jmprovencher/Treasure-Picker-Robot/Remises/Remise 1/tex/Sylvain/systeme_mecanique.tex

La base mécanique du robot est assurée par les différentes plate-formes et tiges filetées fournies pour le projet, il en revient donc à nous de décider de l'agencement de ces composantes afin de produire un robot mécaniquement efficace. De manière à bien modéliser le robot et ainsi faciliter l'installation de futurs équipements, il fut décidé de réaliser une représentation 3D du prototype. La figure \ref{f:CAD} présente le dessin ainsi réalisé, bien que grossier il fut construit à partir de mesures exactes effectuées sur le robot. Ce dessin est très utile pour planifier d'avance l'emplacement des différents systèmes qui seront ajoutés au cours du projet en plus de permettre une meilleure planification de l'organisation des circuits électroniques. 

\medbreak

On peut remarquer que sur ce dessin l'ordinateur embarqué est situé sur la plate-forme centrale, ce choix est justifié par le fait que nous désirons avoir l'électronique le plus proche possible des moteurs DC afin de limiter la longueur des fils. La batterie LiPO représentée par le bloc bleu est positionnée sur la plate-forme la plus basse de manière à assurer un centre de gravité assez bas. Le bloc jaune représente environ les dimensions des circuits électroniques présents sur cet étage du robot. Bien évidemment, toutes ces composantes seront fixées en place. Bien que le pont en H n'est pas observable sur cette image il est important de noter que celui-ci peut être fixé sous la base en cas de besoin. Le préhenseur présenté à la section \ref{s:Prehenseur} est représenté sur le devant du robot, la caméra embarquée est installée directement au-dessus de ce dispositif sur l'étage le plus haut. L'utilisation de ce dessin 3D et d'un autre dessin de la borne de rechargement a aussi permis de mesurer, sans faire de prototype de préhenseur, la hauteur adéquate de la bobine de chargement du condensateur afin de bien aligner les deux dispositifs.

\begin{figure}[htp]
   \centering
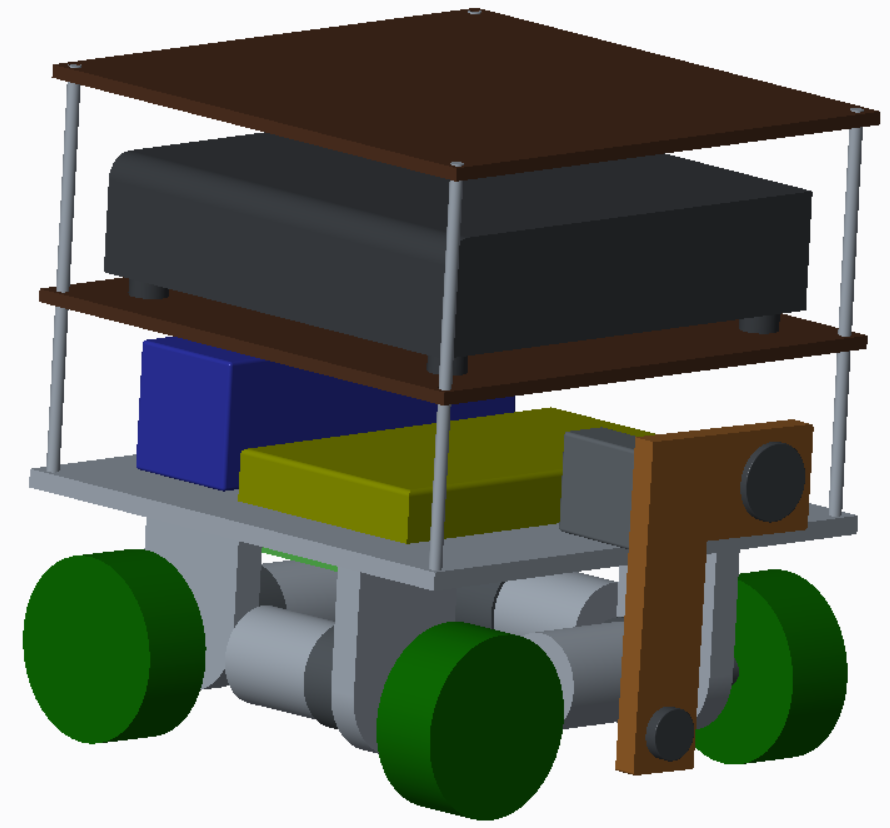
[picture p6: Remises/fig/ROBOT.png]
   
   \caption{Représentation 3D du robot}
   \label{f:CAD}
\end{figure}
