jmprovencher/Treasure-Picker-Robot/Remises/Remise 1/tex/Bourque/comm_sans_fil.tex

La transmission sans-fil du code Manchester est assurée par une combinaison LED-photorécepteur. La LED est située sur le dessus de la station de recharge et le photorécepteur est situé sur le dessus du robot. Ce système de communication sans-fil est limité à des distances relativement faibles, mais le robot étant en contact physique avec la station de recharge, cette contrainte ne pose pas de problème. Le dessin 3D présenté précédemment servira à planifier la disposition exacte de ces composantes une fois les pièces reçues et le concept testé de manière à minimiser les temps de construction et d'assemblage.

\medbreak

La LED est modulé par un microcontrôleur situé sur la station de recharge. Le modèle du microcontrôleur reste à déterminer, mais devra être assez simple et peu coûteux puisque sa tâche sera relativement simple. Ce système de communication est illustré sur le schéma \ref{f:led_robot}.

\medbreak

Le document \cite{COM00} explique brièvement comment réaliser un tel système et est utilisé comme référence pour réaliser notre système.

\begin{figure}[htp]
	\centering
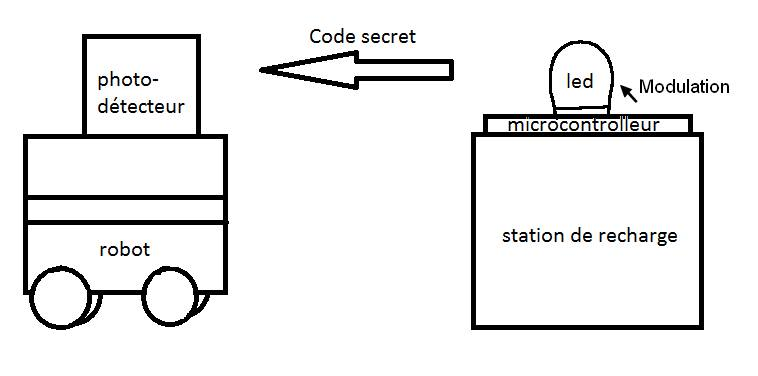
[picture p7: Remises/fig/led_robot.png]
	
	\caption{Communication sans-fil entre la station de recharge et le robot}
	\label{f:led_robot}
\end{figure}
