jmprovencher/Treasure-Picker-Robot/Remises/Remise 1/tex/Main/liste_pieces.tex

\begin{description}
\label{liste_pieces}
	\item[Buck (x3)] \url{http://www.ebay.ca/itm/171445007919?_trksid=p2050601.m570.l6004&_trkparms=gh1g\%3DI171445007919.N41.S2.R2.TR2}
	\item[Batterie LiPo] \url{http://www.hobbyking.com/hobbyking/store/__10284__Turnigy_4500mAh_6S_30C_Lipo_Pack.html}
	\item[Chargeur de batterie LiPO] \url{http://www.hobbyking.com/hobbyking/store/__40270__Hobbyking_8482_T682_AC_6s_10A_90W_Eco_Touch_Balance_Charger_Discharger.html}
	\item[Alarme batterie] \url{http://www.hobbyking.com/hobbyking/store/__74024__HobbyKing_8482_Lipo_Voltage_Checker_2S_8S_.html}
	\item[Arduino Mega] \url{http://www.robotshop.com/ca/en/arduino-mega-2560-microcontroller-rev3.html}
	\item[Servomoteur de contrôle du préhenseur] \url{http://www.robotshop.com/ca/en/hitec-hs-485hb-servo-motor.html}
	\item[Shield pour <<driver>> les moteurs] \url{http://www.robotshop.com/ca/en/motor-shield-kit-arduino-v2.html}
	\item[Électroaimant \textit{Grove}] \url{http://www.seeedstudio.com/wiki/Grove_-_Electromagnet}
\end{description}
