jmprovencher/Treasure-Picker-Robot/Remises/Remise 2/pdf/ContextDiagram.pdf

Business Process Diagram1 Caméra Monde Caméra robot Dispositif de communication sans-fil Serveur des îles Station de base Affichage de la tension du condensateur Affichage de la position et orientation du robot Affichage de la lettre ASCII Affichage de la trajectoire planifiée Rotation des roues Affichage de la forme/couleur de l'île Manipulation du trésor Ordinateur embarqué Microcontrolleur Électroaimant Robot Saisie et relâchement Activation et désactivation Commande de direction/vitesse Appel des méthodes de déplacement par UART Réponse JSON contenant les informations de l'île cible Vidéo fournissant position des trésors, des îles et de la station de recharge Requête HTML utilisant le code | Visual Paradigm Standard Edition(Universite Laval)
