jmprovencher/Treasure-Picker-Robot/Remises/Remise 2/pdf/DPF.pdf

# Obtenir l'île cible Établir une trajectoire de

# Prendre des décisions de manière autonome

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
# Alimenter le robot de manière autonome

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
# Naviguer autour des îles

5

5

5

# Éviter contact avec les murs

5

5

# Communiquer sans fil entre les éléments du système

5

5

5

# Protéger l'alimentation du robot avec des fusibles et interrupteurs

5

# Alimenter la station de recharge avec alimentation 5V, 1A

5

5

# Respecter un budget maximal de 300$ (sans PCB)

4

2

3

# Actualiser affichage à une fréquence minimale de 0.2Hz

5

5

5

5

5

1

# Effectuer au moins une routine complète en dix minutes

2

4

3

4

3

3

3

# Affichage de la tension du condensateur en temps réel sur la station de base

5

5
Finir le projet d'ici le 17 avril.

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
# Afficher la position avec une précision de position minimalement de 15 centimètres

5

5

# Monter l'électronique du robot sur un PCB

4

4

3

4 Tension entre 21V et 30V | 1 seule permise

# Communiquer entre les éléments du

sécuritaire aux éléments du système | autonome | | | autonome | | de façon autonome | de la station de base | système
Afficher la tension des cellules de la batterie Signaler une alerte en cas de danger Alimenter adéquatement chaque élément du système Protéger adéquatement les composantes électroniques internes | Démarrer le robot sans intervention extérieure Confirmer le départ de la routine à partir de la station Confirmer la fin de l'exécution ainsi que le temps écoulé avec l'usager | Décoder le code Manchester Envoyer une requête au serveur des îles Interpréter la réponse du serveur en format JSON | Analyser les flux vidéo des deux caméras pour identifier la cible façon autonome Alimenter le robot avec une batterie Établir une trajectoire vers un trésor puis vers une île Déterminer la commande idéale pour suivre la trajectoire | Avancer le robot Tourner le robot | Saisir un trésor Soulever un trésor Déposer un trésor sur l'île prescrite | Recevoir la charge par induction Lire la tension aux bornes du condensateur Se retirer lorsque la charge est complète | Afficher les trajectoires ⁽prévue et réelle⁾ sur une image de la table Afficher la position et l'orientation du robot Afficher la tension aux bornes du condensateur Afficher la forme ou la couleur de l'île cible | Communiquer entre l'ordinateur du robot et le microcontrôlleur Communiquer sans fil entre l'ordinateur du robot et la station de base Recevoir sans fil le code Manchester Communiquer sans fil entre l'ordinateur du robot et le serveur d'îles

# Se déplacer de façon

# Manipuler les trésors Gérer le condensateur

# Fournir une alimentation adéquate et

# Fonctionner de façon

# Offrir une interface graphique à l'aide
