jmprovencher/Treasure-Picker-Robot/Remises/Remise 3/tex/Main/annexe.tex

%!TEX encoding = IsoLatin

%
% Annexe "Liste des sigles et des acronymes"
%

\chapter{Liste des sigles et des acronymes}
\label{Sigles}

\begin{flushleft}
   \begin{tabular}{@{}ll}
      \textbf{CAO}        & Conception Assistée par Ordinateur \\
   \end{tabular}
\end{flushleft}
