jmprovencher/Treasure-Picker-Robot/Remises/Remise 2/pdf/PlanIntegration.pdf

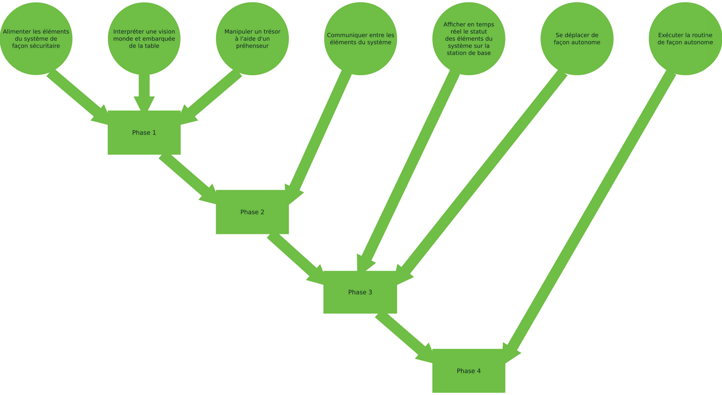
[picture p38: page 1]
