jmprovencher/Treasure-Picker-Robot/Remises/Remise 2/tex/Main/Diagrammes.tex

\chapter{Diagrammes}
\label{s:Diagrammes}

\section{Diagramme des fonctionnalités}
\label{s:Diagramme_fonctionnalites}

\begin{figure}[htp]
   \centering
   
   \caption{Diagramme des fonctionnalités}
   \label{f:diagramme_fonctionnalites}
\end{figure}

\section{Diagramme physique}
\label{s:diagramme_physique}

\begin{figure}[htp]
   \centering
   
   \caption{Diagramme physique}
   \label{f:diagramme_physique}
\end{figure}

\section{Diagramme de séquences}
\label{s:diagramme_sequence}

Les figures \ref{f:diagramme_sequence1} à \ref{f:diagramme_sequence4} correspondent aux diagrammes de séquences.

\begin{figure}[htp]
   \centering
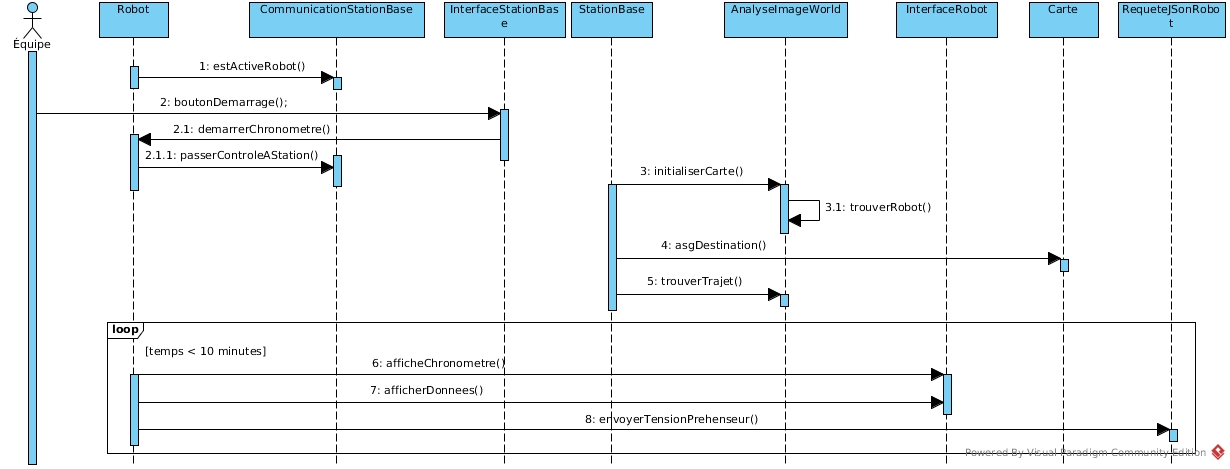
[picture p39: Remises/Remise 2/fig/demarageRobot.jpg]
   
   \caption{Diagramme de séquences: démarage du robot}
   \label{f:diagramme_sequence1}
\end{figure}

\begin{figure}[htp]
   \centering
   
   \caption{Diagramme de séquences: Deplacement du trésor}
   \label{f:diagramme_sequence2}
\end{figure}

\begin{figure}[htp]
   \centering
   
   \caption{Diagramme de séquences: initialisation de la carte}
   \label{f:diagramme_sequence3}
\end{figure}

\begin{figure}[htp]
   \centering
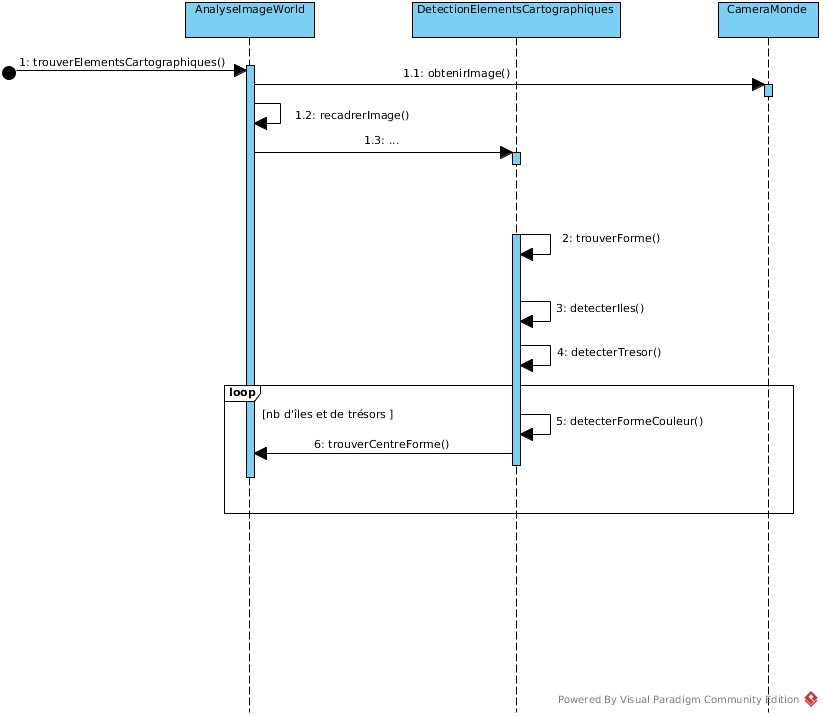
[picture p40: Remises/Remise 2/fig/trouverIleOuTresor.jpg]
   
   \caption{Diagramme de séquences: trouver les îles et trésors}
   \label{f:diagramme_sequence4}
\end{figure}
