jmprovencher/Treasure-Picker-Robot/glo/BlackPearl/Cropped.png

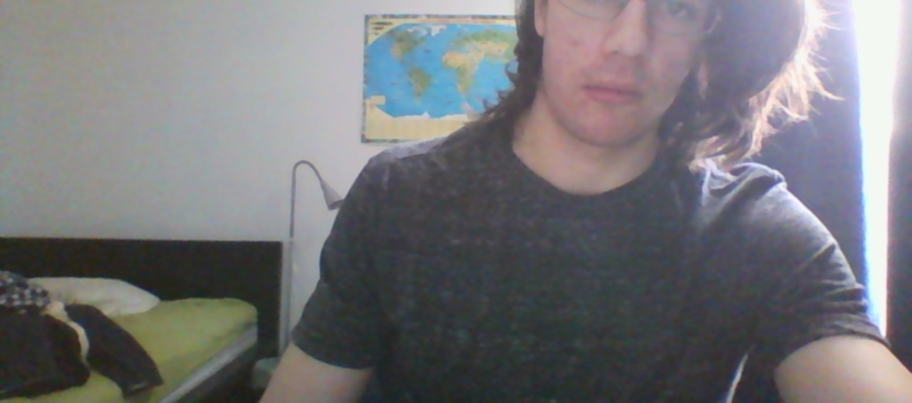
glo/BlackPearl/Cropped.png
