jmprovencher/Treasure-Picker-Robot/glo/BlackPearl/imageReelle.png

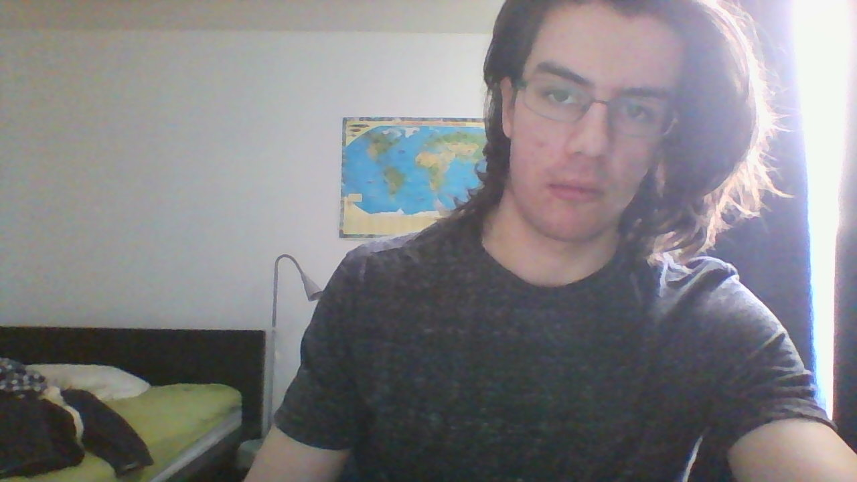
glo/BlackPearl/imageReelle.png
