jmprovencher/Treasure-Picker-Robot/glo/BlackPearl/images/robot.png

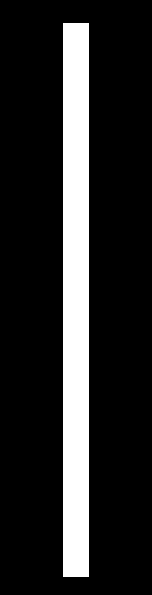
glo/BlackPearl/images/robot.png
