jmprovencher/Treasure-Picker-Robot/glo/BlackPearl/images/table2/detection2.png

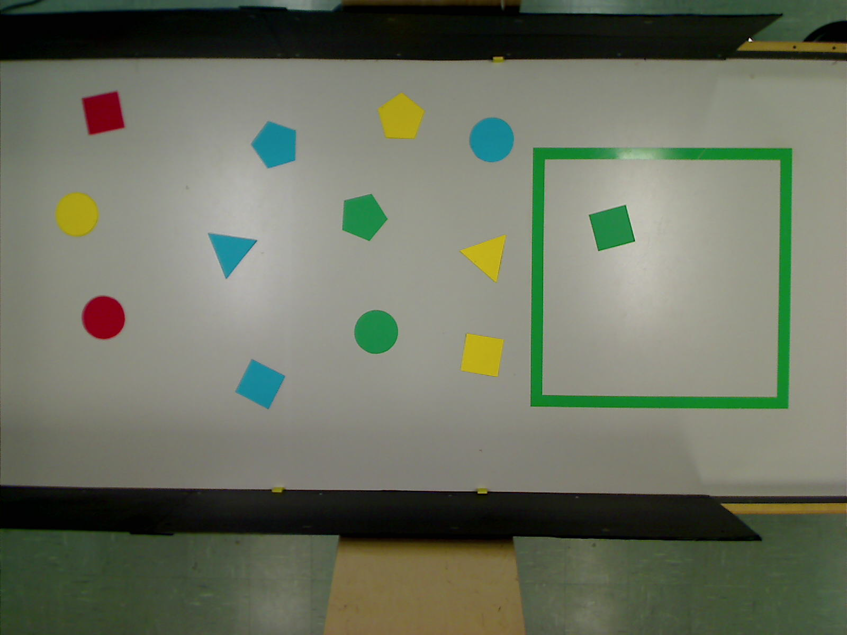
glo/BlackPearl/images/table2/detection2.png
