jmprovencher/Treasure-Picker-Robot/glo/BlackPearl/images/table2/trajet1.png

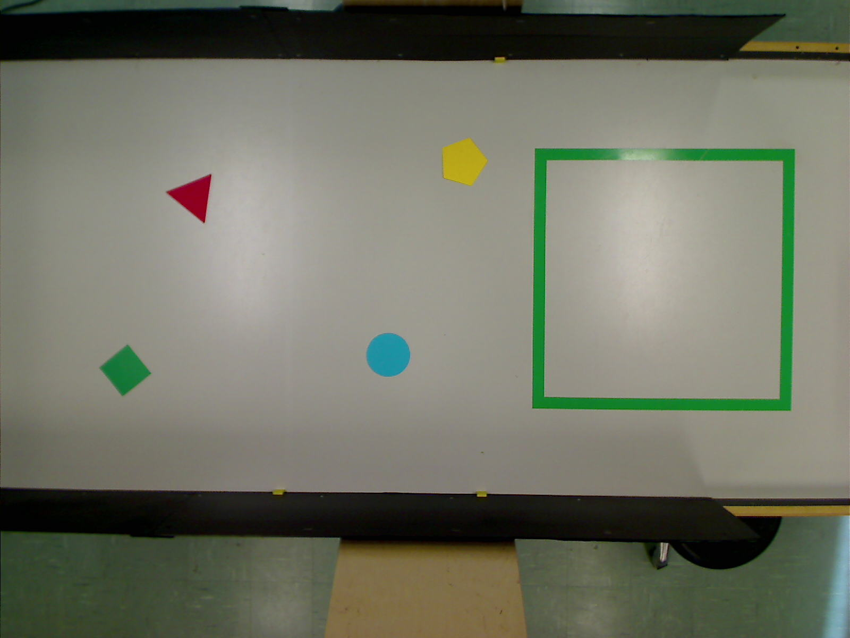
glo/BlackPearl/images/table2/trajet1.png
