jmprovencher/Treasure-Picker-Robot/glo/BlackPearl/images/table2/trajet2.png

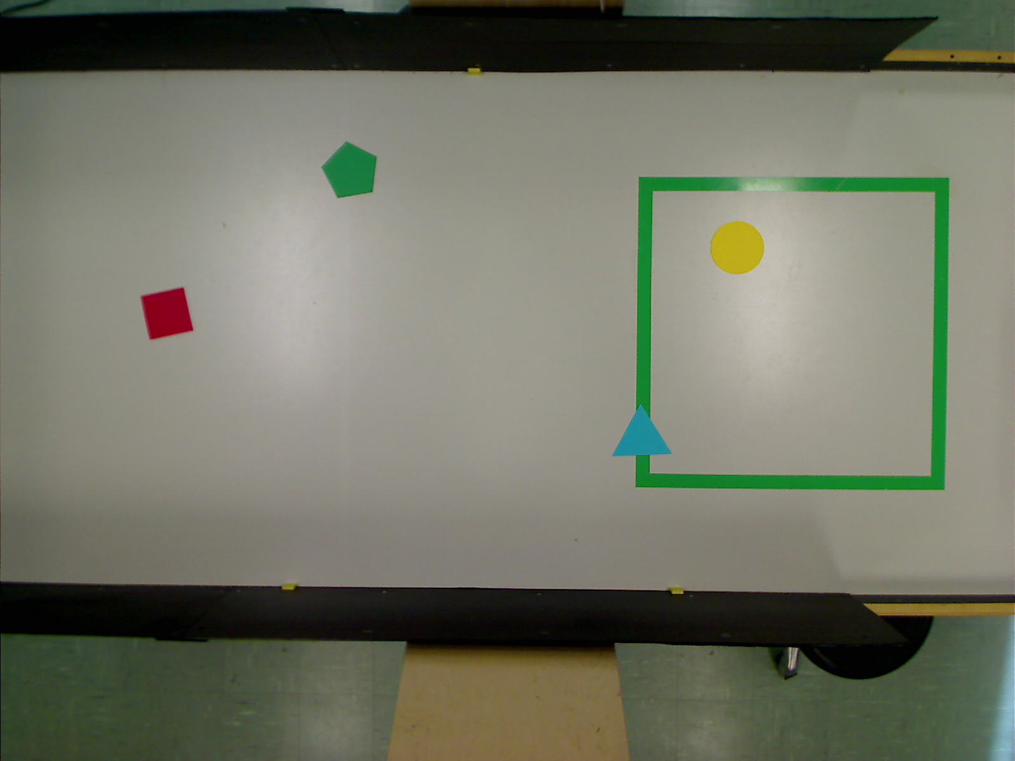
glo/BlackPearl/images/table2/trajet2.png
