jmprovencher/Treasure-Picker-Robot/glo/BlackPearl/stationbase/interface/Cropped.png

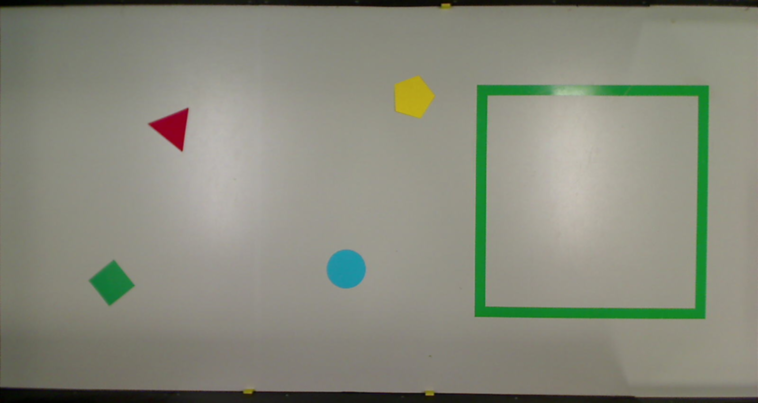
glo/BlackPearl/stationbase/interface/Cropped.png
