jmprovencher/Treasure-Picker-Robot/glo/obtenirImageWorld/ilebleue.png

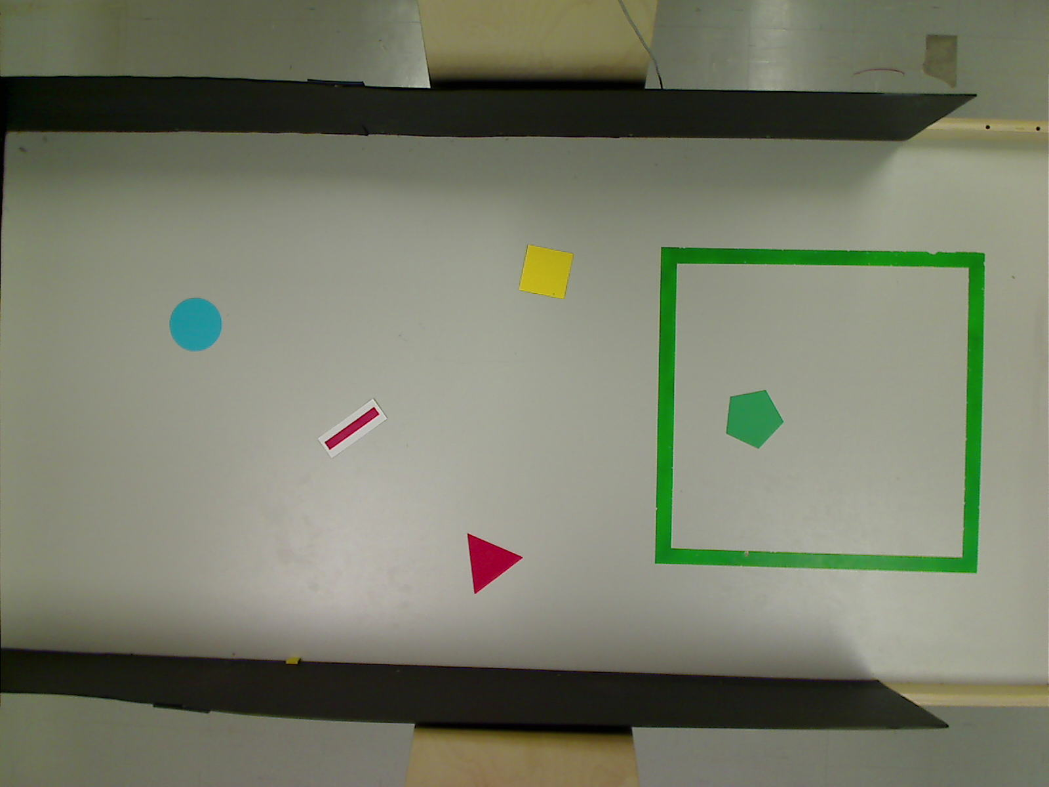
glo/obtenirImageWorld/ilebleue.png
