jmprovencher/Treasure-Picker-Robot/glo/obtenirImageWorld/ilejaune.png

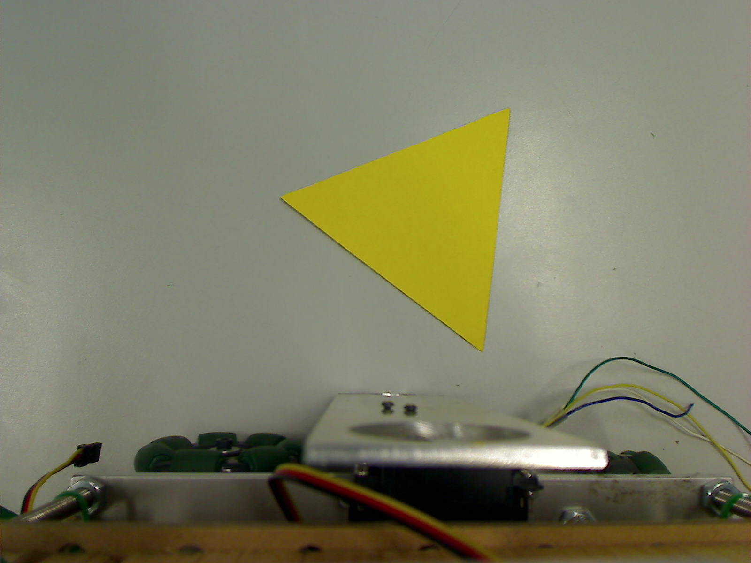
glo/obtenirImageWorld/ilejaune.png
