jmprovencher/Treasure-Picker-Robot/glo/obtenirImageWorld/ilerouge.png

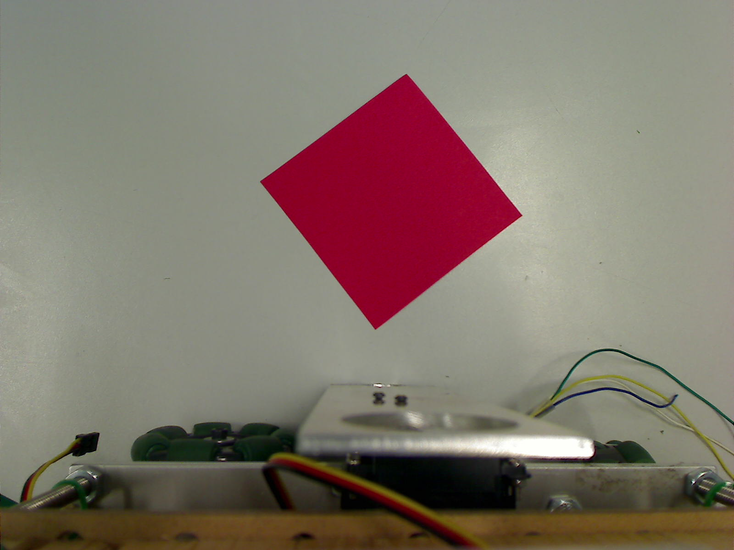
glo/obtenirImageWorld/ilerouge.png
