jmprovencher/Treasure-Picker-Robot/glo/obtenirImageWorld/ileverte.png

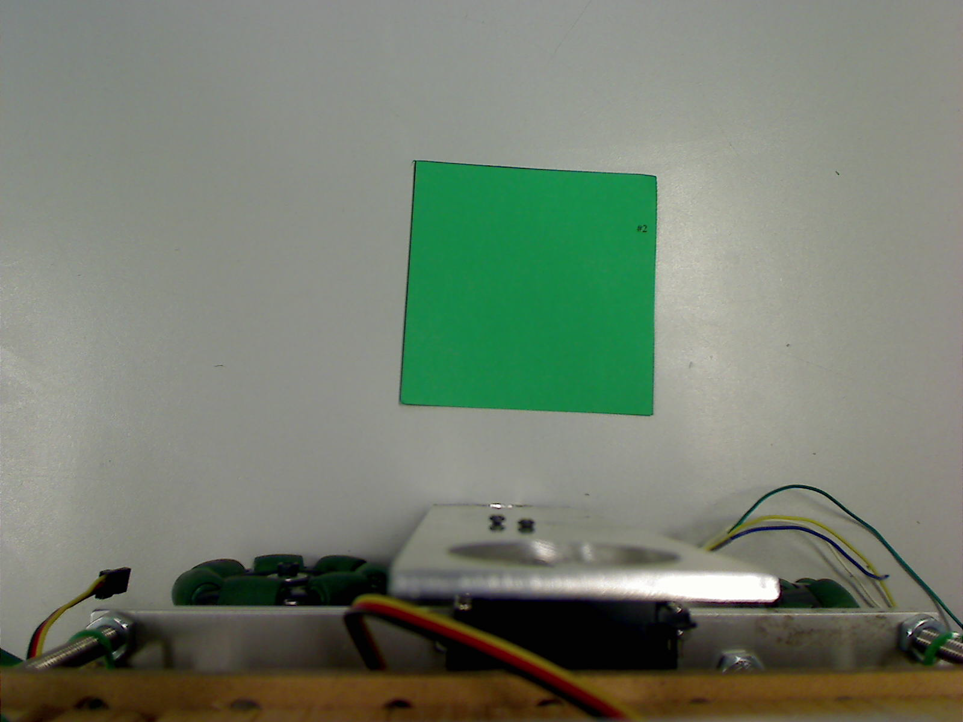
glo/obtenirImageWorld/ileverte.png
