jmprovencher/Treasure-Picker-Robot/Remises/Remise 1/fig/contextDiagram.PNG

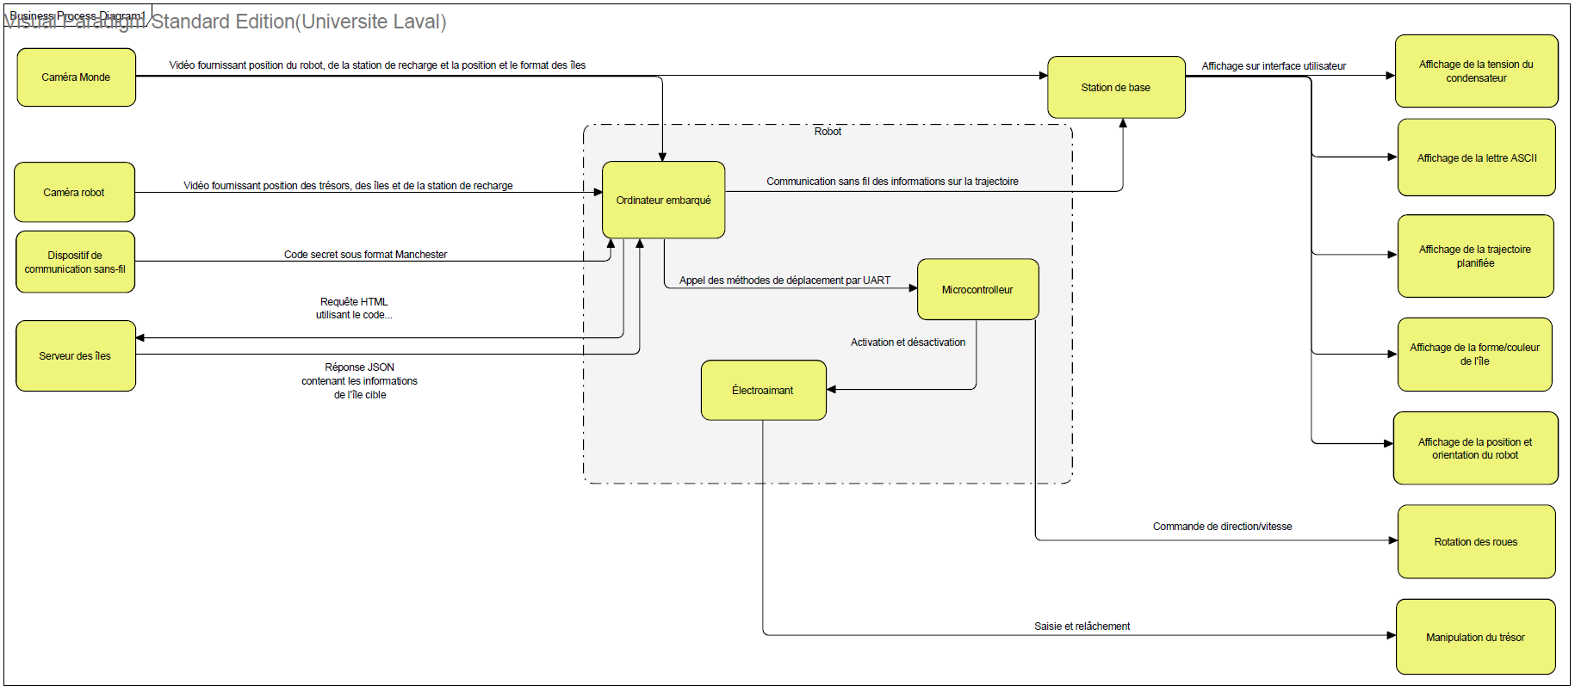
Remises/Remise 1/fig/contextDiagram.PNG
