jmprovencher/Treasure-Picker-Robot/Remises/Remise 1/fig/deplaceTresor.jpg

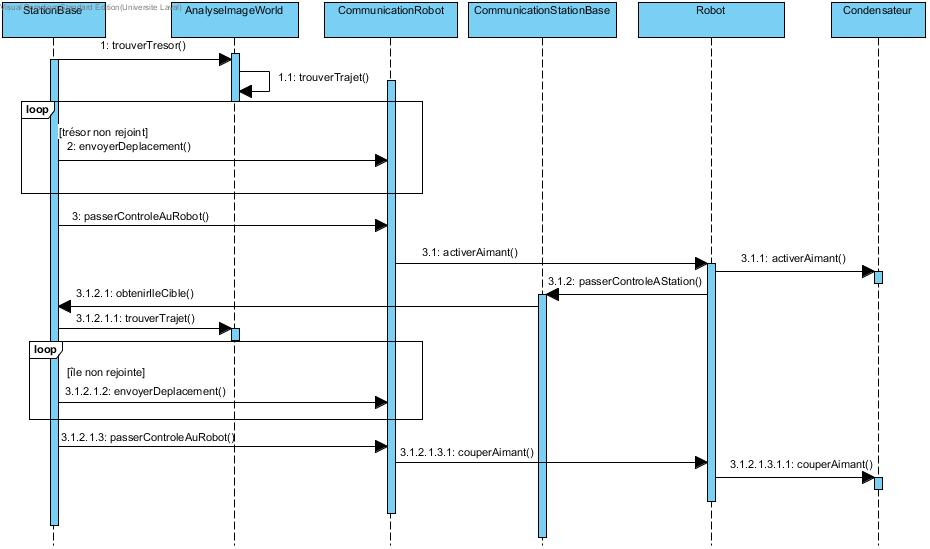
Remises/Remise 1/fig/deplaceTresor.jpg
