jmprovencher/Treasure-Picker-Robot/Remises/Remise 1/fig/descriptionPropriete.png

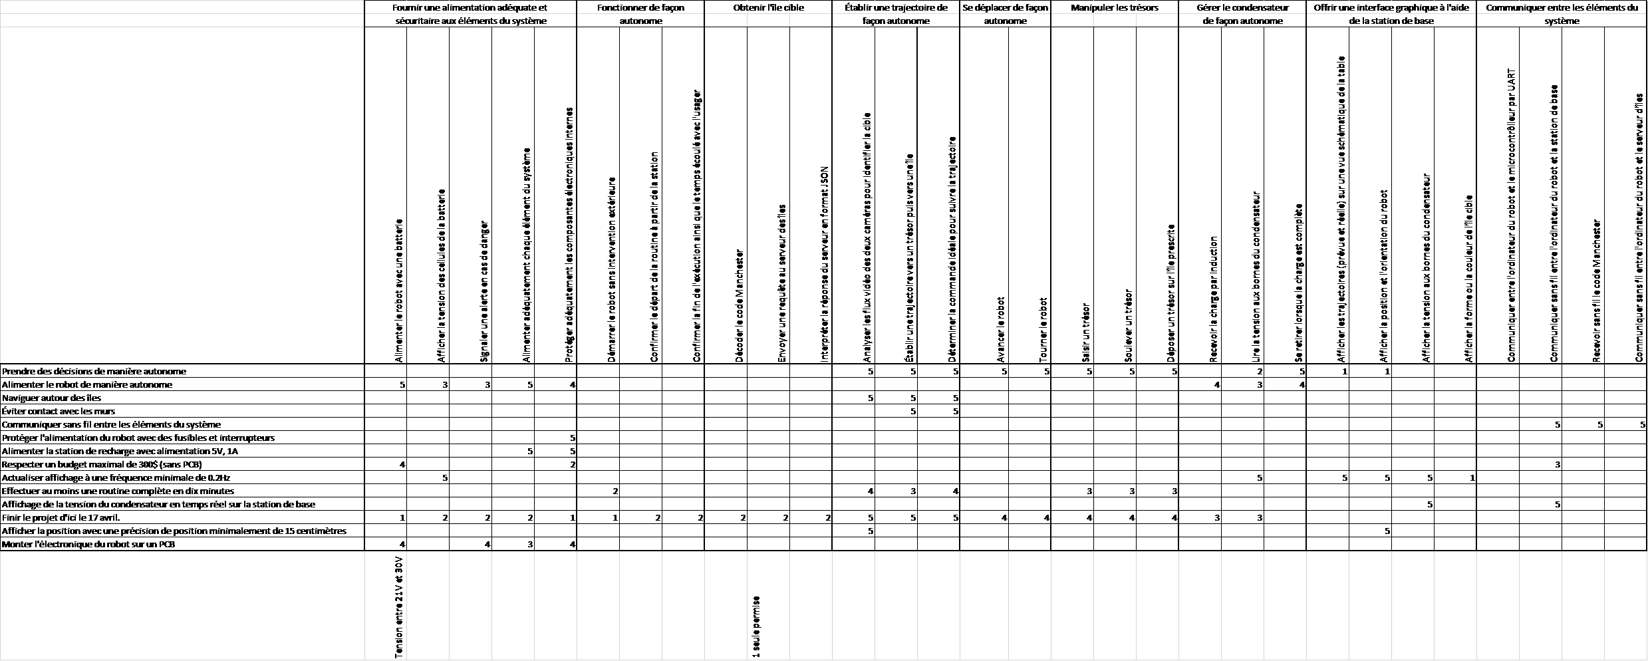
Remises/Remise 1/fig/descriptionPropriete.png
