jmprovencher/Treasure-Picker-Robot/Remises/Remise 2/fig/deplaceTresor.jpg

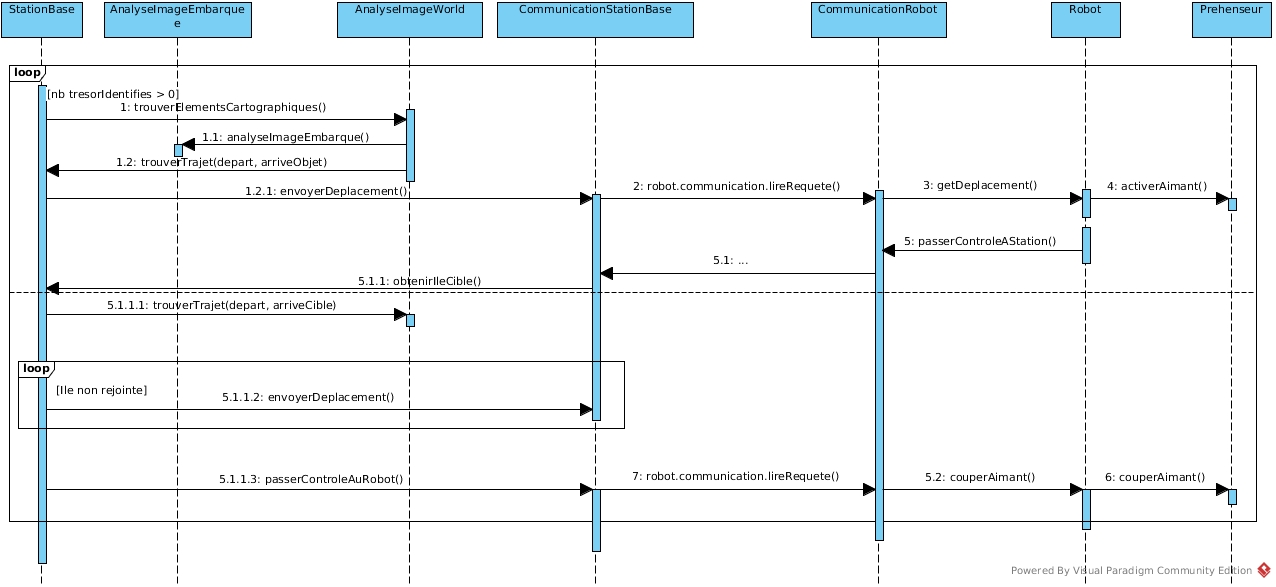
Remises/Remise 2/fig/deplaceTresor.jpg
