jmprovencher/Treasure-Picker-Robot/Remises/Remise 2/fig/DiagrameDeClasse.jpg

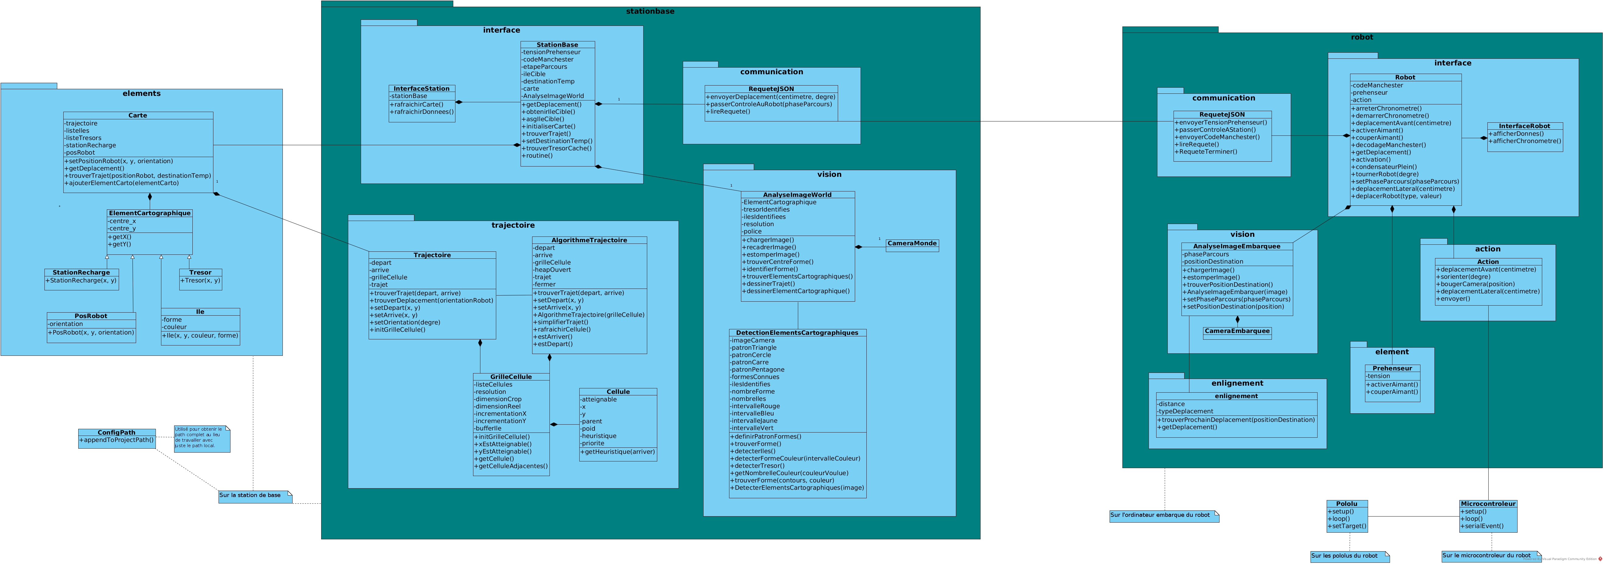
Remises/Remise 2/fig/DiagrameDeClasse.jpg
