jmprovencher/Treasure-Picker-Robot/Remises/Remise 2/fig/initCarte.jpg

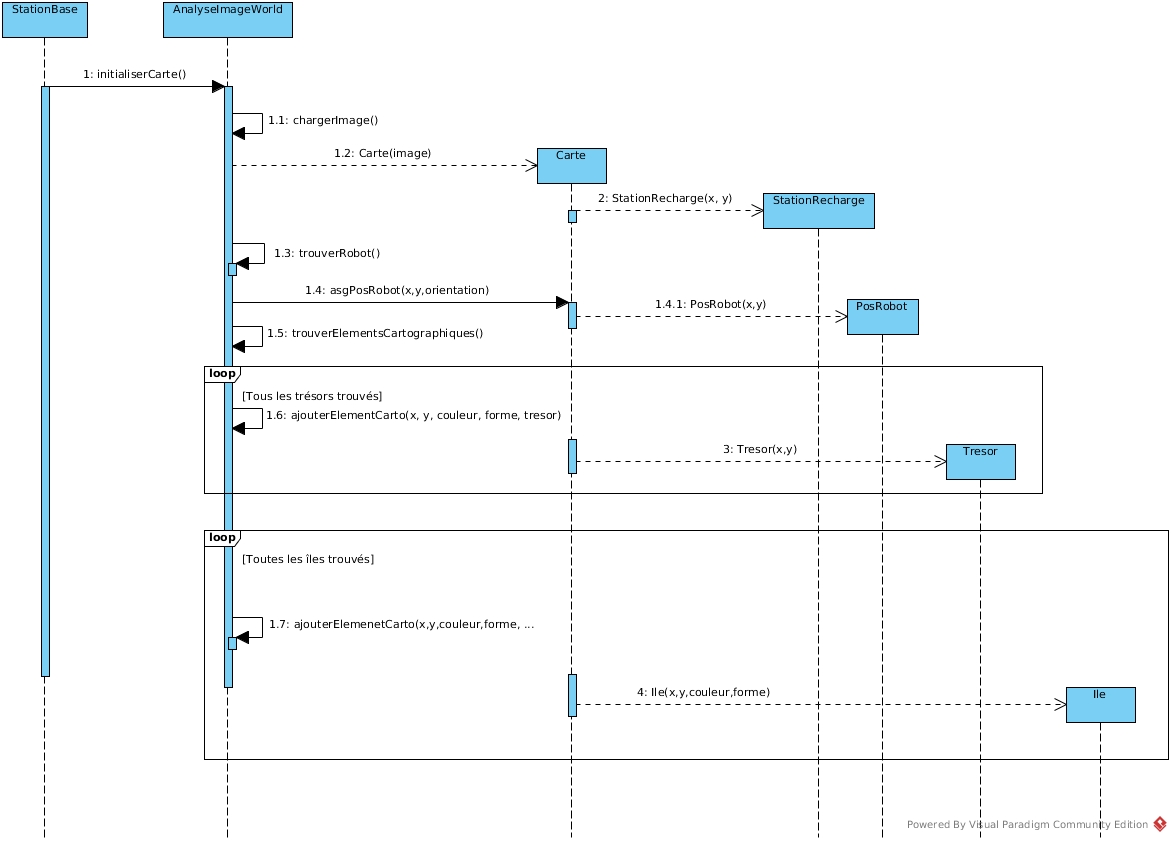
Remises/Remise 2/fig/initCarte.jpg
