jmprovencher/Treasure-Picker-Robot/glo/BlackPearl/images/camera_robot/iles/test_image9.png

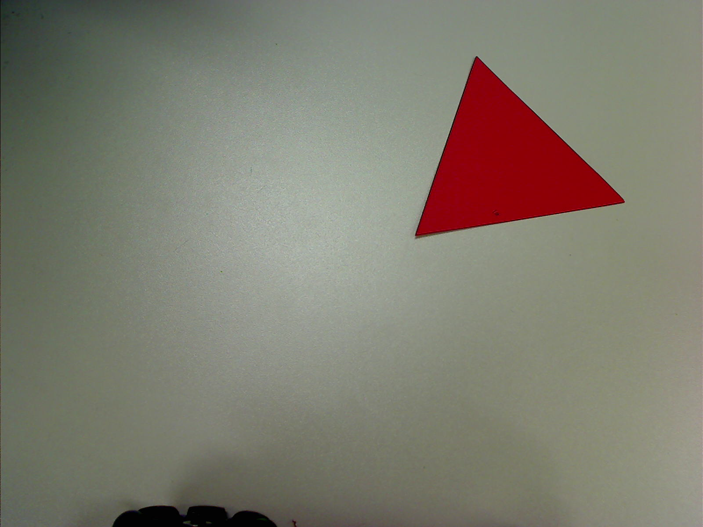
glo/BlackPearl/images/camera_robot/iles/test_image9.png
