jmprovencher/Treasure-Picker-Robot/glo/BlackPearl/images/camera_robot/iles/test_image11.png

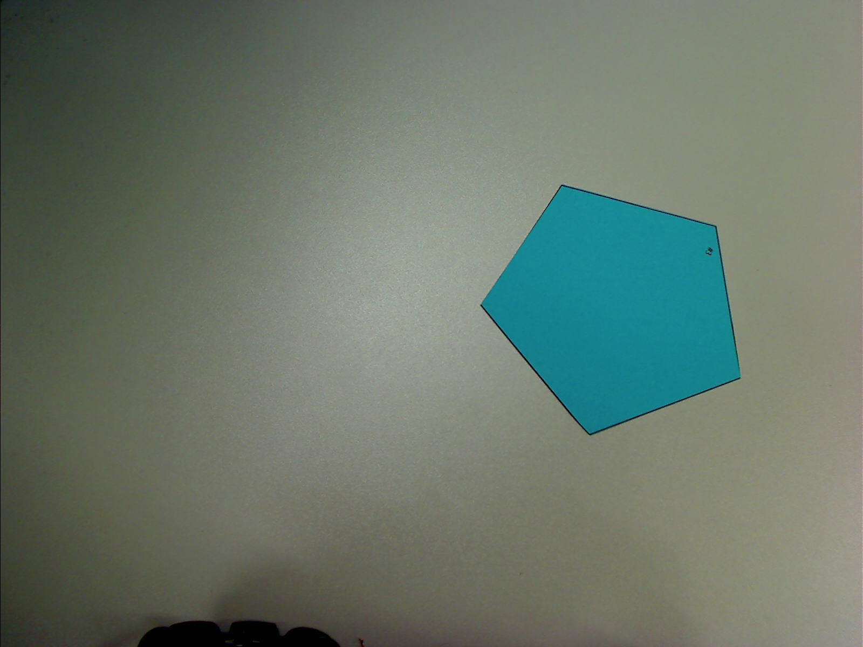
glo/BlackPearl/images/camera_robot/iles/test_image11.png
