jmprovencher/Treasure-Picker-Robot/glo/BlackPearl/images/camera_robot/iles/test_image13.png

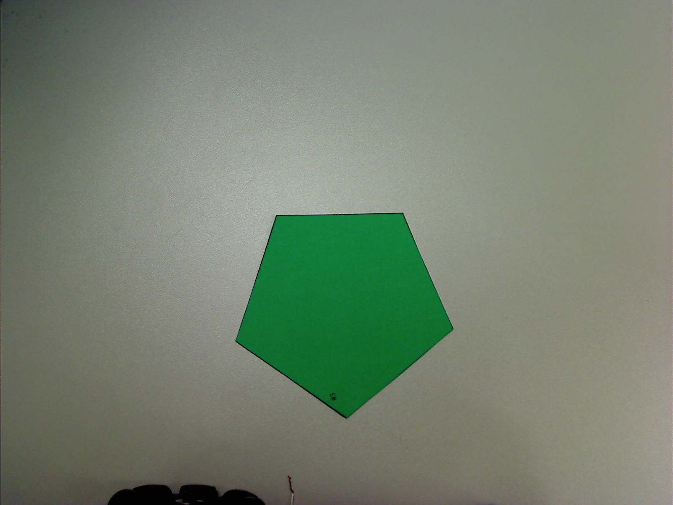
glo/BlackPearl/images/camera_robot/iles/test_image13.png
