jmprovencher/Treasure-Picker-Robot/glo/BlackPearl/images/camera_robot/iles/test_image14.png

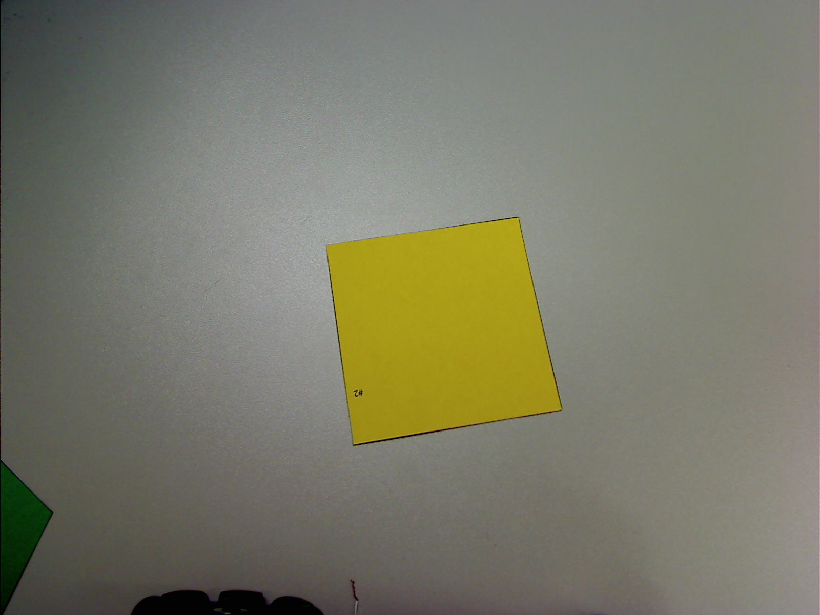
glo/BlackPearl/images/camera_robot/iles/test_image14.png
