jmprovencher/Treasure-Picker-Robot/glo/BlackPearl/images/camera_robot/iles/test_image19.png

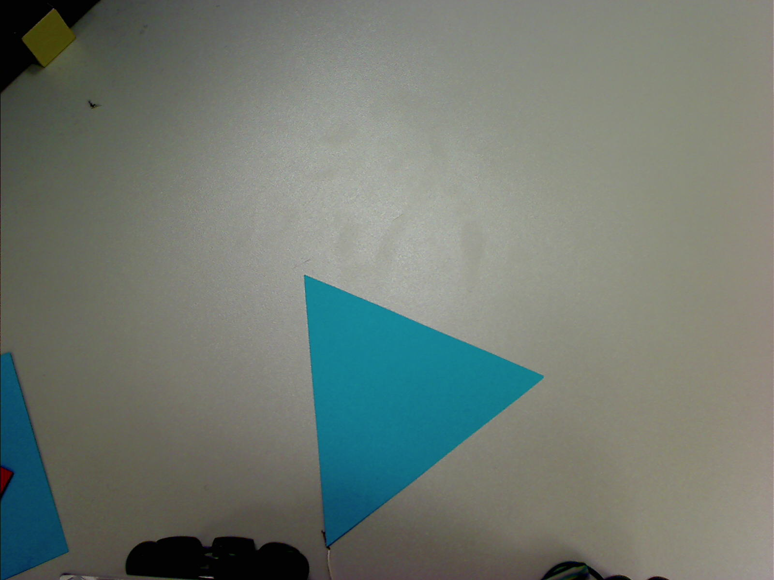
glo/BlackPearl/images/camera_robot/iles/test_image19.png
