jmprovencher/Treasure-Picker-Robot/glo/BlackPearl/images/camera_robot/tresors/test_image2.png

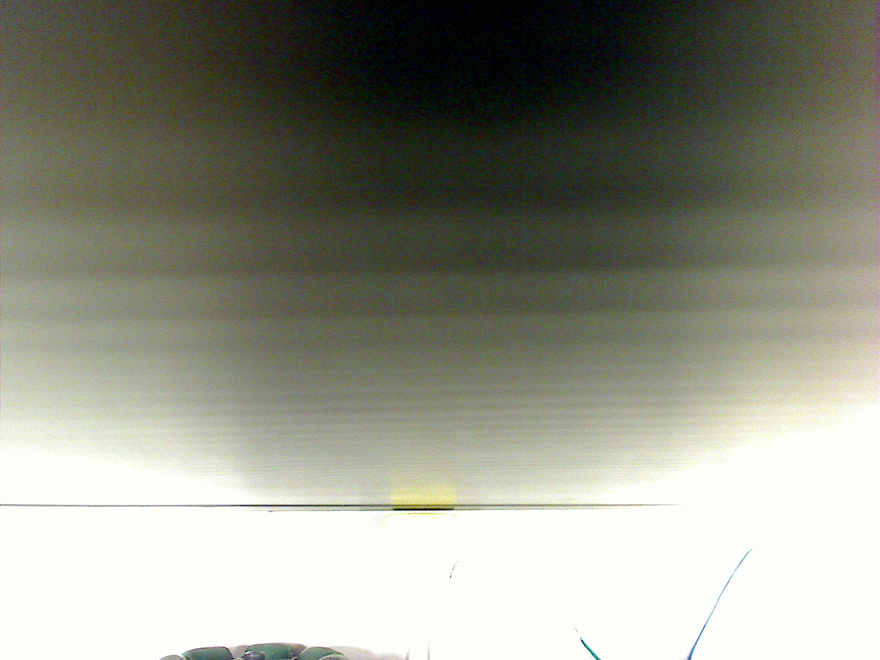
glo/BlackPearl/images/camera_robot/tresors/test_image2.png
