jmprovencher/Treasure-Picker-Robot/glo/BlackPearl/images/image_testunitaire.png

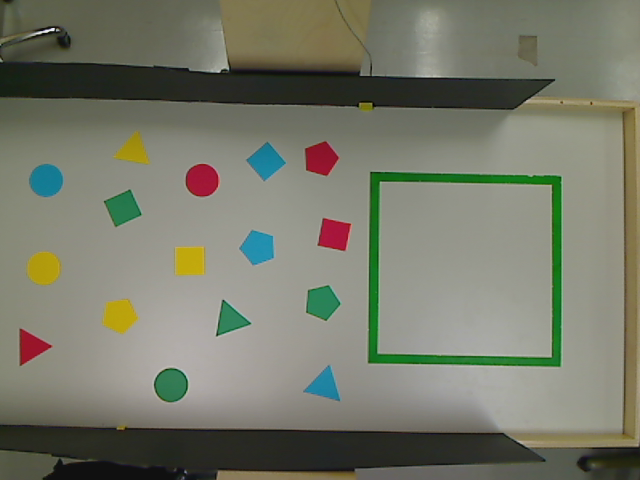
glo/BlackPearl/images/image_testunitaire.png
