jmprovencher/Treasure-Picker-Robot/glo/BlackPearl/images/orientation/test_image19.png

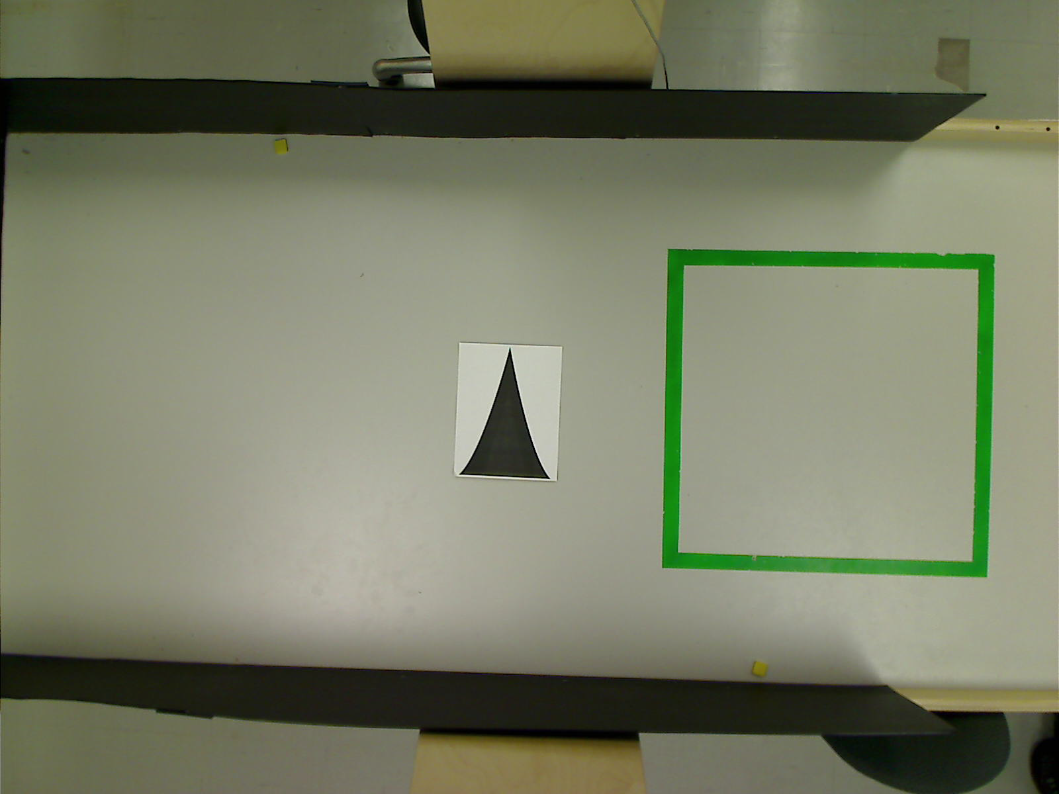
glo/BlackPearl/images/orientation/test_image19.png
