jmprovencher/Treasure-Picker-Robot/glo/BlackPearl/images/res++/test_image20.png

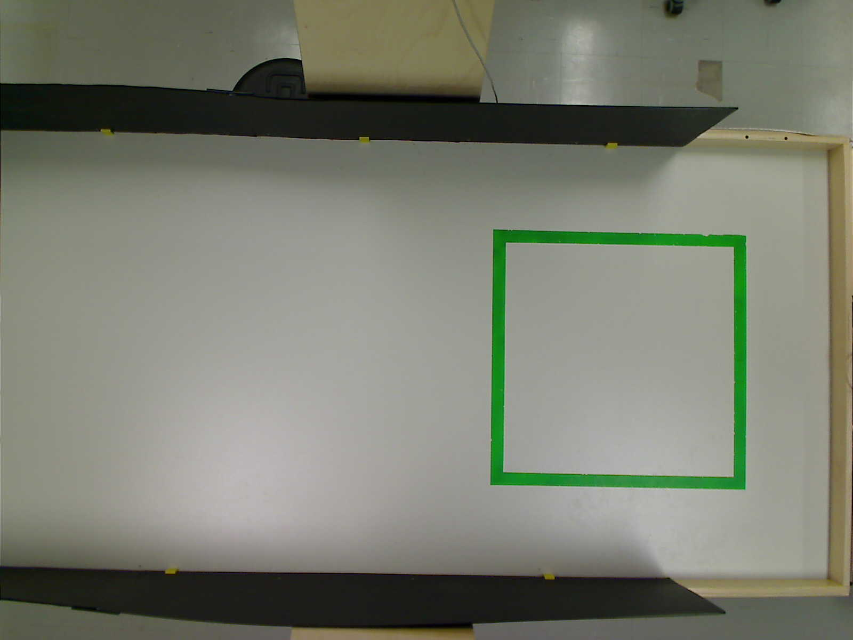
glo/BlackPearl/images/res++/test_image20.png
