jmprovencher/Treasure-Picker-Robot/glo/BlackPearl/images/table2/test-vert1.png

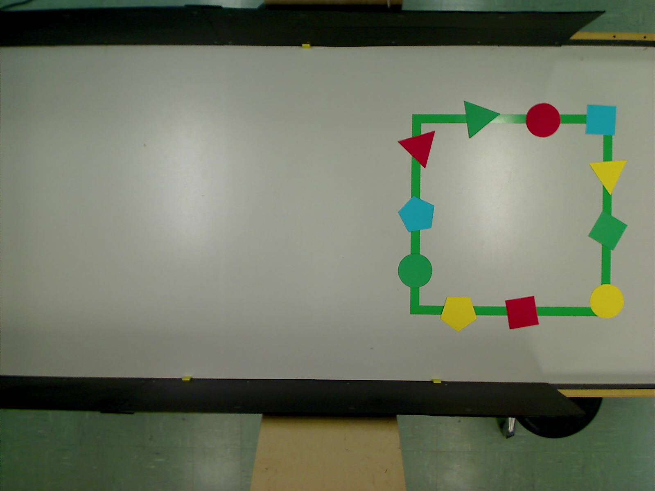
glo/BlackPearl/images/table2/test-vert1.png
