jmprovencher/Treasure-Picker-Robot/glo/BlackPearl/images/table2/test_image1.png

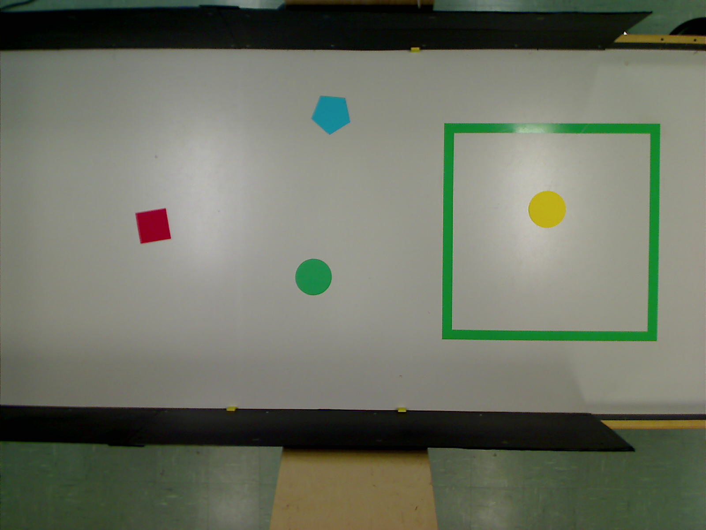
glo/BlackPearl/images/table2/test_image1.png
