jmprovencher/Treasure-Picker-Robot/glo/BlackPearl/images/test_image1.png

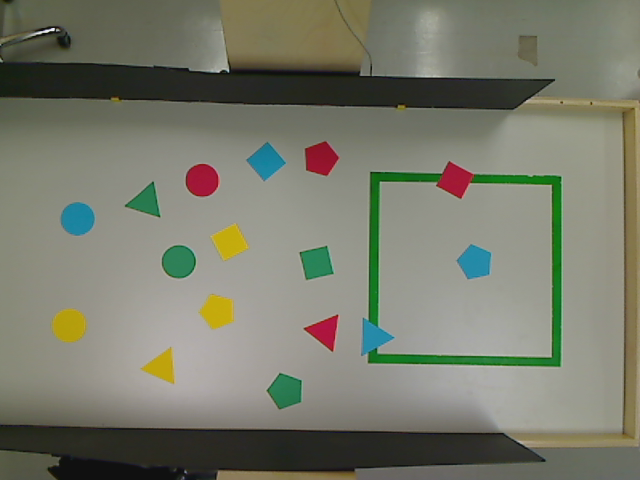
glo/BlackPearl/images/test_image1.png
