jmprovencher/Treasure-Picker-Robot/glo/BlackPearl/images/test_image2.png

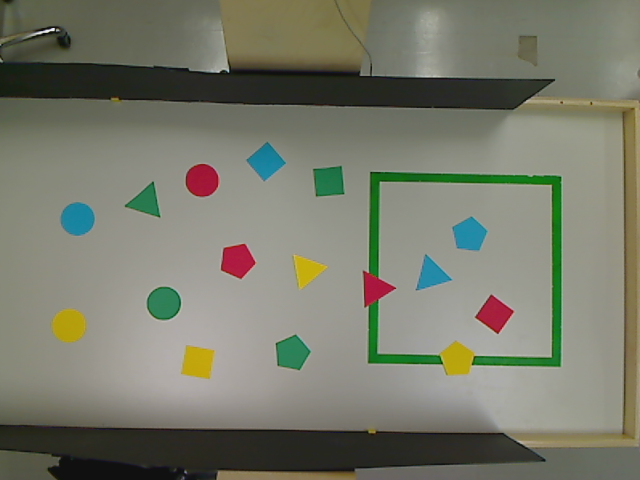
glo/BlackPearl/images/test_image2.png
