jmprovencher/Treasure-Picker-Robot/glo/BlackPearl/images/test_image7.png

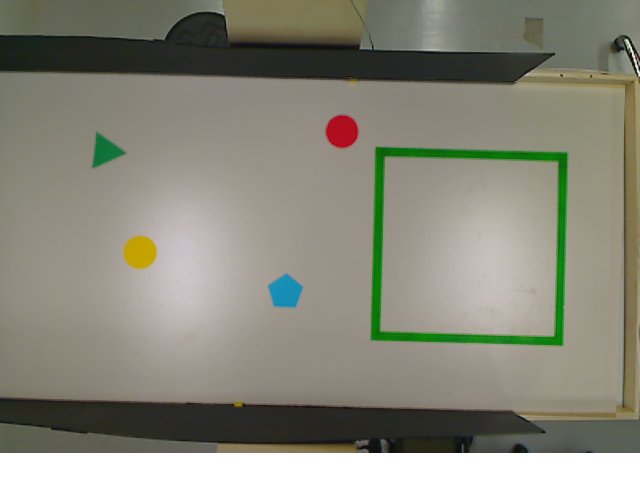
glo/BlackPearl/images/test_image7.png
