jmprovencher/Treasure-Picker-Robot/glo/BlackPearl/images/test_image8.png

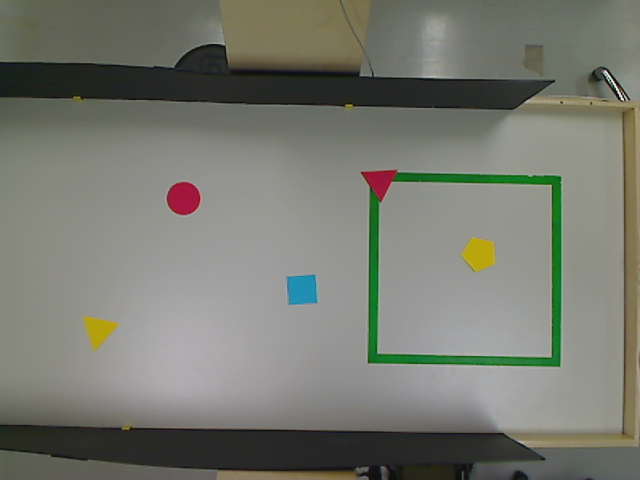
glo/BlackPearl/images/test_image8.png
