jmprovencher/Treasure-Picker-Robot/glo/obtenirImageWorld/test_image19.png

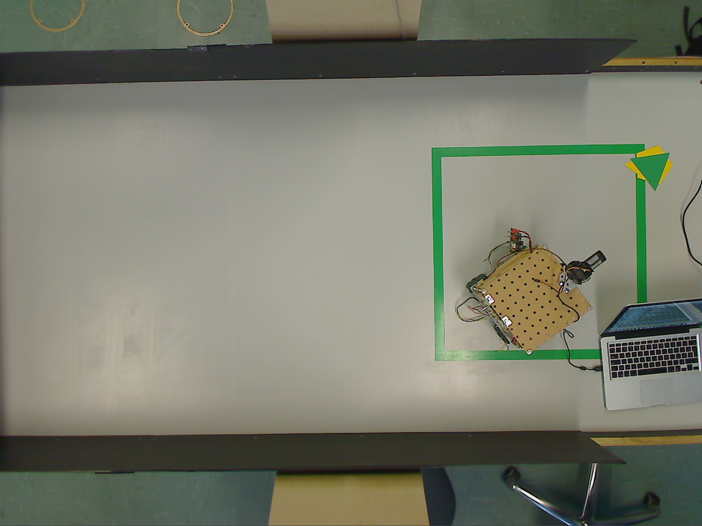
glo/obtenirImageWorld/test_image19.png
