jmprovencher/Treasure-Picker-Robot/Remises/Remise 2/pdf/DiagrammeFonctionnalites.pdf

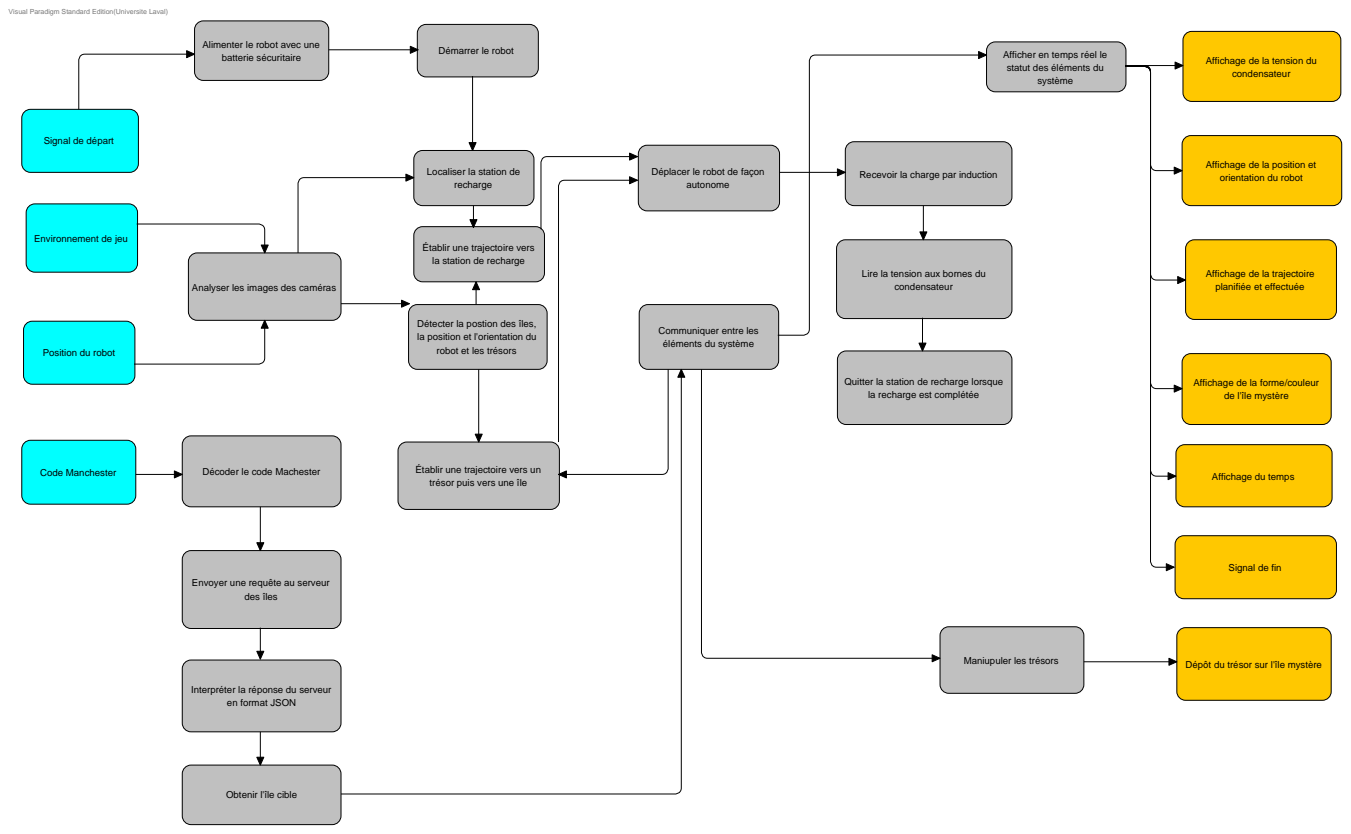
[picture p85: page 1]
Code Manchester; autonome; des îles

Visual Paradigm Standard Edition(Universite Laval)

Alimenter le robot avec une
batterie sécuritaire

Démarrer le robot

Afficher en temps réel le
statut des éléments du
système

Affichage de la tension du
condensateur

Signal de départ

Affichage de la position et
orientation du robot

Localiser la station de
recharge

Déplacer le robot de façon

Recevoir la charge par induction

Environnement de jeu

Établir une trajectoire vers
la station de recharge

Lire la tension aux bornes du

Affichage de la trajectoire
planifiée et effectuée

Analyser les images des caméras

Détecter la postion des îles,
la position et l'orientation du
robot et les trésors

Communiquer entre les
éléments du système

Position du robot

Quitter la station de recharge lorsque
la recharge est complétée

Affichage de la forme/couleur
de l'île mystère

Décoder le code Machester

Établir une trajectoire vers un
trésor puis vers une île

Affichage du temps

Signal de fin

Envoyer une requête au serveur

Maniupuler les trésors

Dépôt du trésor sur l'île mystère

Interpréter la réponse du serveur

en format JSON

Obtenir l'île cible
