jmprovencher/Treasure-Picker-Robot/Remises/Remise 2/pdf/casutilisation.pdf

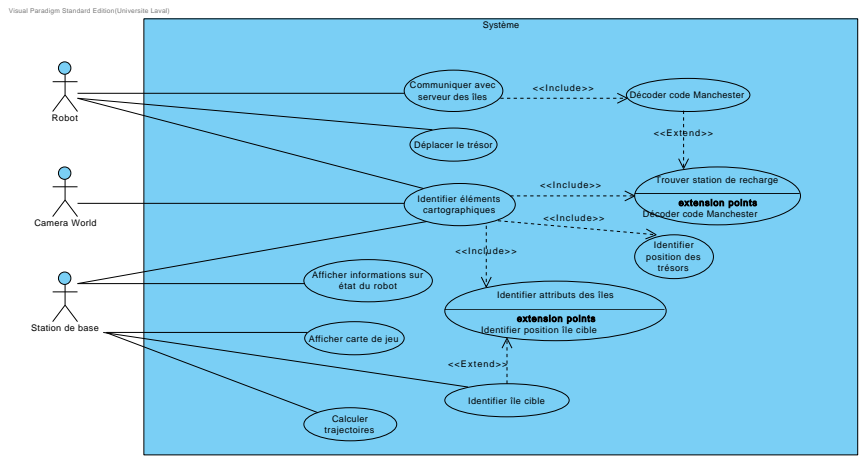
[picture p87: page 1]
Système; extension points; Identifier position des trésors; Identifier éléments cartographiques; Calculer trajectoires; Camera World; Robot; <<Include>>; <<Extend>>

Visual Paradigm Standard Edition(Universite Laval)

Communiquer avec
serveur des îles

Décoder code Manchester

Déplacer le trésor

Trouver station de recharge

Afficher informations sur
état du robot

Identifier attributs des îles

Station de base

Identifier position île cible

Afficher carte de jeu

Identifier île cible
