jmprovencher/Treasure-Picker-Robot/glo/BlackPearl/robot/communication/TCPClient.py

import socket
import json


class TCPClient:
    def __init__(self):
        self.s = socket.socket()
        self.port = 60000
        self.host = '10.248.187.169'
        #self.host = '192.168.1.37' #If on embedded computer in local network
        self.connectionEstablished = self._connectToServer()

    def _connectToServer(self):
        while True:
            try:
                self.s.connect((self.host, self.port))
                break
            except Exception as e:
                print("Connection failed with %s:%d. Exception is %s" % (self.host, self.port, e))
        return True

    def sendFile(self, filename,):
        f = open(filename, 'r')
        data = f.read()
        while data:
            self.s.send(data)
            print('Sent ', repr(data))
            data = f.read()
        f.close()
        print('Done sending file')
        return 1

    def receiveFile(self):
        with open('received_file.json', 'wb') as f:
            print 'file opened'
            print('receiving data...')
            data = self.s.recv(1024)
            print('data=%s', data)
            # write data to a file
            f.write(data)

        f.close()
        print('Successfully got the file')
        json_data = open('received_file.json').read()
        if json_data == '':
            print ('Empty file')
            return -1
        else:
            try:
                data = json.loads(json_data)
            except:
                print('No JSON object was found')
            return data


    def closeConnection(self):
        self.s.close()
        print('Closed Connection with Base Station')
